maperales/MAPESYNTH/SOFTWARE/formas.c

/*
 * formas.c
 *
 *  Created on: 10 jun. 2022
 *      Author: ManoloP
 */

#include "formas.h"


const int SAMPLES [NUMINST][128]=
{
 {0, 25, 50, 75, 100, 124, 149, 172, 196, 219, 241, 263, 284, 305, 325, 344,
  362, 379, 396, 411, 426, 439, 452, 463, 473, 482, 490, 497, 502, 506, 510, 511,
  512, 511, 510, 506, 502, 497, 490, 482, 473, 463, 452, 439, 426, 411, 396, 379,
  362, 344, 325, 305, 284, 263, 241, 219, 196, 172, 149, 124, 100, 75, 50, 25,
  0, -25, -50, -75, -100, -124, -149, -172, -196, -219, -241, -263, -284, -305, -325, -344,
  -362, -379, -396, -411, -426, -439, -452, -463, -473, -482, -490, -497, -502, -506, -510, -511,
  -512, -511, -510, -506, -502, -497, -490, -482, -473, -463, -452, -439, -426, -411, -396, -379,
  -362, -344, -325, -305, -284, -263, -241, -219, -196, -172, -149, -124, -100, -75, -50, -25,
 },
 {
  0, 42, 83, 124, 163, 202, 240, 275, 309, 341, 371, 398, 422, 444, 463, 478,
  491, 501, 508, 511, 512, 510, 504, 496, 486, 472, 457, 439, 420, 398, 375, 351,
  326, 300, 274, 247, 220, 193, 167, 141, 117, 93, 71, 50, 30, 12, -4, -18,
  -30, -41, -49, -55, -60, -62, -63, -62, -60, -56, -50, -44, -36, -28, -19, -10,
  0, 10, 19, 28, 36, 44, 50, 56, 60, 62, 63, 62, 60, 55, 49, 41,
  30, 18, 4, -12, -30, -50, -71, -93, -117, -141, -167, -193, -220, -247, -274, -300,
  -326, -351, -375, -398, -420, -439, -457, -472, -486, -496, -504, -510, -512, -511, -508, -501,
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
                    (int)(1244.50793 Hz),
                    (int)(1318.51023 Hz),
                    (int)(1396.91293 Hz),
                    (int)(1479.97769 Hz),
                    (int)(1567.98174 Hz),
                    (int)(1661.21879 Hz)  //LA4
};
