maperales/MAPESYNTH/SOFTWARE/formas.h

#define NUMINST 8


#define     Hz  *128L*256/20000  // Normalizado de frecuencias
#define OFFSET_NOTA 36          //Primera nota en la tabla: MIDI 36

extern const int SAMPLES [NUMINST][128];
extern const int Freq[57];
